AoToS/Load_Cell-board/hardware/2023-03-20-17-40-10.png

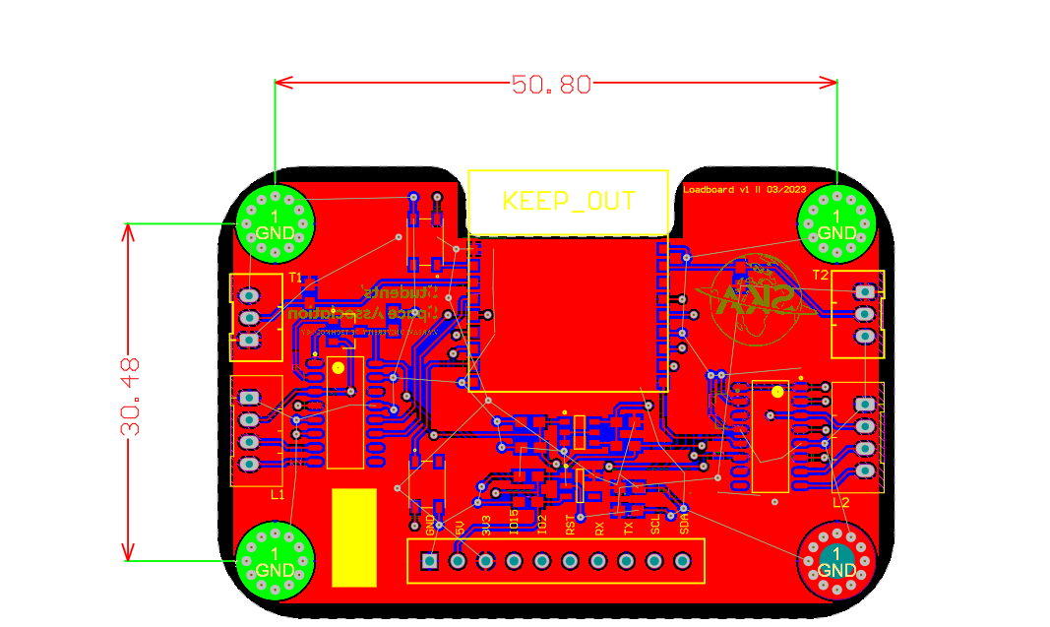
hardware/2023-03-20-17-40-10.png
