AoToS/Load_Cell-board/hardware/2023-03-20-18-51-30.png

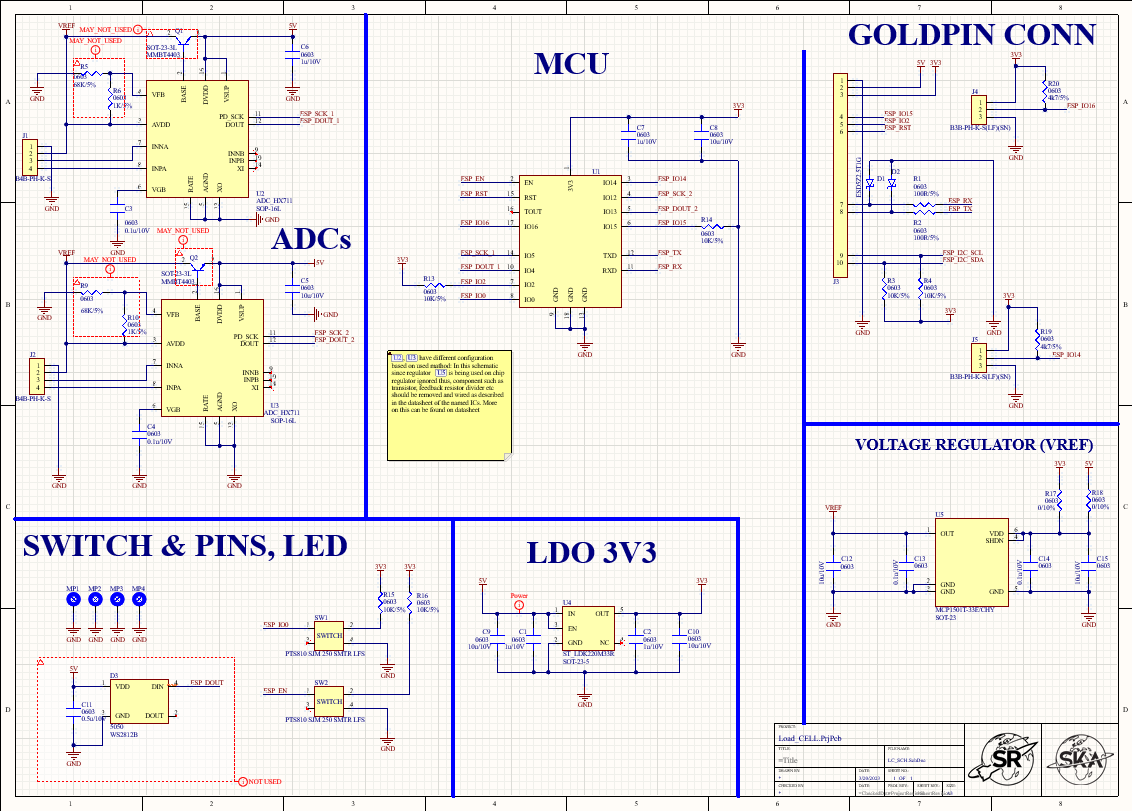
hardware/2023-03-20-18-51-30.png
